zzeneg/pica40/images/3d-printed-case-front.jpg

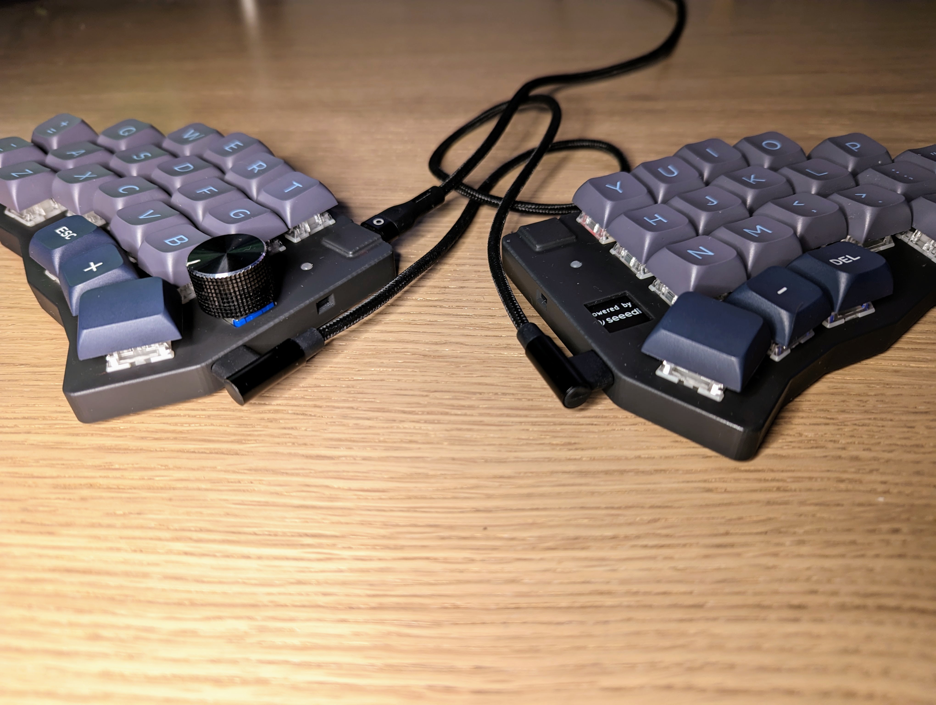
images/3d-printed-case-front.jpg
